RandBeyy/Standalone_AVR_Programmer/software/include/Signatures.h

// Signatures.h
//
// Signatures and extra information for known chips
//
// Author: Nick Gammon

#include "avr/pgmspace.h"

// copy of fuses/lock bytes found for this processor
uint8_t fuses [5];

// meaning of positions in above array
enum {
      lowFuse,
      highFuse,
      extFuse,
      lockByte,
      calibrationByte
};

// structure to hold signature and other relevant data about each chip
typedef struct {
   uint8_t sig [3];                // chip signature
   char desc [14];              // fixed array size keeps chip names in PROGMEM
   unsigned long flashSize;     // how big the flash is (bytes)
   unsigned int baseBootSize;   // base bootloader size (others are multiples of 2/4/8)
   unsigned long pageSize;      // flash programming page size (bytes)
   uint8_t fuseWithBootloaderSize; // ie. one of: lowFuse, highFuse, extFuse
   bool timedWrites;            // true if pollUntilReady won't work by polling the chip
} signatureType;

const unsigned long kb = 1024;
const uint8_t NO_FUSE = 0xFF;


// see Atmega datasheets
const signatureType signatures[] PROGMEM =
  {
//     signature        description   flash size   bootloader  flash  fuse     timed
//                                                     size    page    to      writes
//                                                             size   change

  // Attiny84 family
  { { 0x1E, 0x91, 0x0B }, "ATtiny24",   2 * kb,           0,   32,   NO_FUSE,  false  },
  { { 0x1E, 0x92, 0x07 }, "ATtiny44",   4 * kb,           0,   64,   NO_FUSE,  false  },
  { { 0x1E, 0x93, 0x0C }, "ATtiny84",   8 * kb,           0,   64,   NO_FUSE,  false  },

  // Attiny85 family
  { { 0x1E, 0x91, 0x08 }, "ATtiny25",   2 * kb,           0,   32,   NO_FUSE,  false  },
  { { 0x1E, 0x92, 0x06 }, "ATtiny45",   4 * kb,           0,   64,   NO_FUSE,  false  },
  { { 0x1E, 0x93, 0x0B }, "ATtiny85",   8 * kb,           0,   64,   NO_FUSE,  false  },

  // Atmega328 family
  { { 0x1E, 0x92, 0x0A }, "ATmega48PA",   4 * kb,         0,    64,  NO_FUSE,  false  },
  { { 0x1E, 0x93, 0x0F }, "ATmega88PA",   8 * kb,       256,   128,  extFuse,  false },
  { { 0x1E, 0x94, 0x0B }, "ATmega168PA", 16 * kb,       256,   128,  extFuse,  false },
  { { 0x1E, 0x94, 0x06 }, "ATmega168V",  16 * kb,       256,   128,  extFuse,  false },
  { { 0x1E, 0x95, 0x0F }, "ATmega328P",  32 * kb,       512,   128,  highFuse, false },
  { { 0x1E, 0x95, 0x16 }, "ATmega328PB", 32 * kb,       512,   128,  highFuse, false },
  { { 0x1E, 0x95, 0x14 }, "ATmega328",   32 * kb,       512,   128,  highFuse, false },

  // Atmega644 family
  { { 0x1E, 0x94, 0x0A }, "ATmega164P",   16 * kb,      256,   128,  highFuse, false },
  { { 0x1E, 0x95, 0x08 }, "ATmega324P",   32 * kb,      512,   128,  highFuse, false },
  { { 0x1E, 0x96, 0x0A }, "ATmega644P",   64 * kb,   1 * kb,   256,  highFuse, false },

  // Atmega2560 family
  { { 0x1E, 0x96, 0x08 }, "ATmega640",    64 * kb,   1 * kb,   256,  highFuse, false },
  { { 0x1E, 0x97, 0x03 }, "ATmega1280",  128 * kb,   1 * kb,   256,  highFuse, false },
  { { 0x1E, 0x97, 0x04 }, "ATmega1281",  128 * kb,   1 * kb,   256,  highFuse, false },
  { { 0x1E, 0x98, 0x01 }, "ATmega2560",  256 * kb,   1 * kb,   256,  highFuse, false },

  { { 0x1E, 0x98, 0x02 }, "ATmega2561",  256 * kb,   1 * kb,   256,  highFuse, false },

  // AT90USB family
  { { 0x1E, 0x93, 0x82 }, "At90USB82",    8 * kb,       512,   128,  highFuse, false },
  { { 0x1E, 0x94, 0x82 }, "At90USB162",  16 * kb,       512,   128,  highFuse, false },

  // Atmega32U2 family
  { { 0x1E, 0x93, 0x89 }, "ATmega8U2",    8 * kb,       512,   128,  highFuse, false },
  { { 0x1E, 0x94, 0x89 }, "ATmega16U2",  16 * kb,       512,   128,  highFuse, false },
  { { 0x1E, 0x95, 0x8A }, "ATmega32U2",  32 * kb,       512,   128,  highFuse, false },

  // Atmega32U4 family -  (datasheet is wrong about flash page size being 128 words)
  { { 0x1E, 0x94, 0x88 }, "ATmega16U4",  16 * kb,       512,   128,  highFuse, false },
  { { 0x1E, 0x95, 0x87 }, "ATmega32U4",  32 * kb,       512,   128,  highFuse, false },

  // ATmega1284P family
  { { 0x1E, 0x97, 0x05 }, "ATmega1284P", 128 * kb,   1 * kb,   256,  highFuse, false },
  { { 0x1E, 0x97, 0x06 }, "ATmega1284",  128 * kb,   1 * kb,   256,  highFuse, false },

  // ATtiny4313 family
  { { 0x1E, 0x91, 0x0A }, "ATtiny2313A",   2 * kb,        0,    32,  NO_FUSE,  false   },
  { { 0x1E, 0x92, 0x0D }, "ATtiny4313",    4 * kb,        0,    64,  NO_FUSE,  false   },

  // ATtiny13 family
  { { 0x1E, 0x90, 0x07 }, "ATtiny13A",     1 * kb,        0,    32,  NO_FUSE,  false  },

   // Atmega8A family
  { { 0x1E, 0x93, 0x07 }, "ATmega8A",      8 * kb,      256,    64,  highFuse, true },

  // ATmega64rfr2 family
  { { 0x1E, 0xA6, 0x02 }, "ATmega64rfr2",  256 * kb, 1 * kb,   256,  highFuse, false },
  { { 0x1E, 0xA7, 0x02 }, "ATmega128rfr2", 256 * kb, 1 * kb,   256,  highFuse, false },
  { { 0x1E, 0xA8, 0x02 }, "ATmega256rfr2", 256 * kb, 1 * kb,   256,  highFuse, false },

  };  // end of signatures
